CamBitter/bike-theft-deterrent-system.github.io/images/armedScreen.jpeg

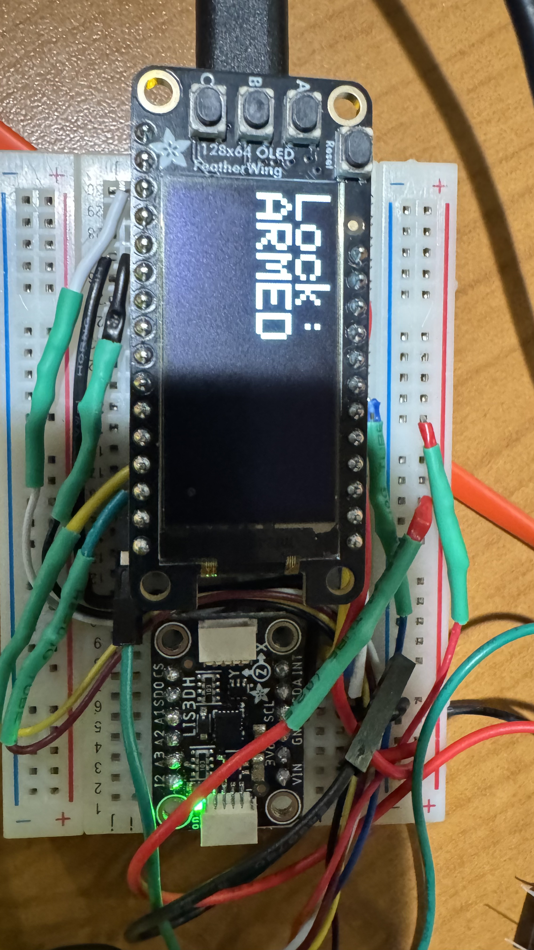
images/armedScreen.jpeg
