CamBitter/bike-theft-deterrent-system.github.io/images/boxWork.jpeg

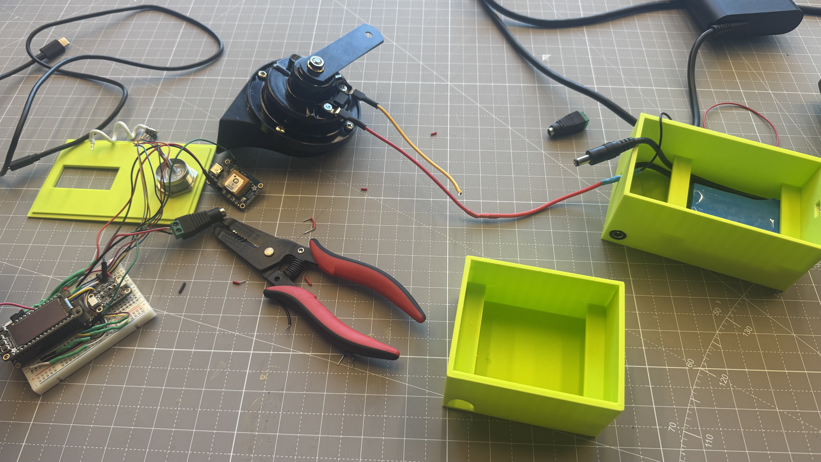
images/boxWork.jpeg
