CamBitter/bike-theft-deterrent-system.github.io/images/GPSwork.jpeg

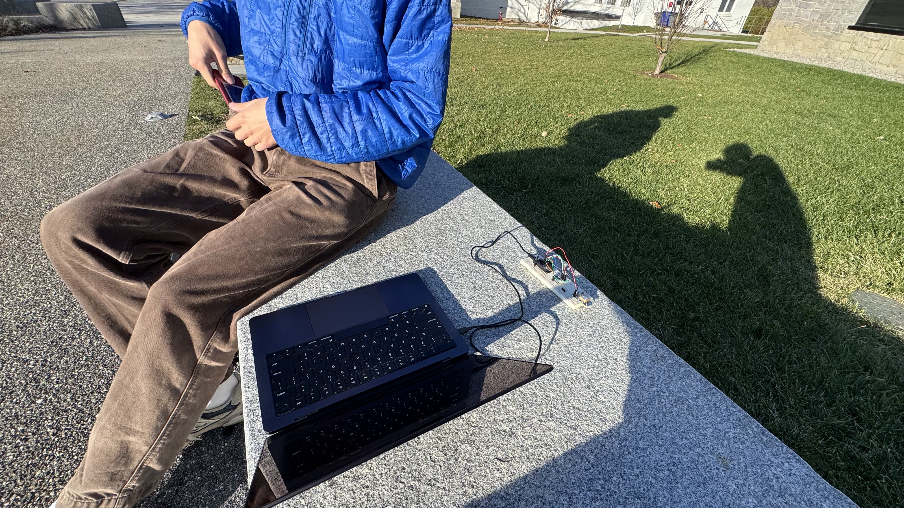
images/GPSwork.jpeg
