CamBitter/bike-theft-deterrent-system.github.io/images/procBomb.PNG

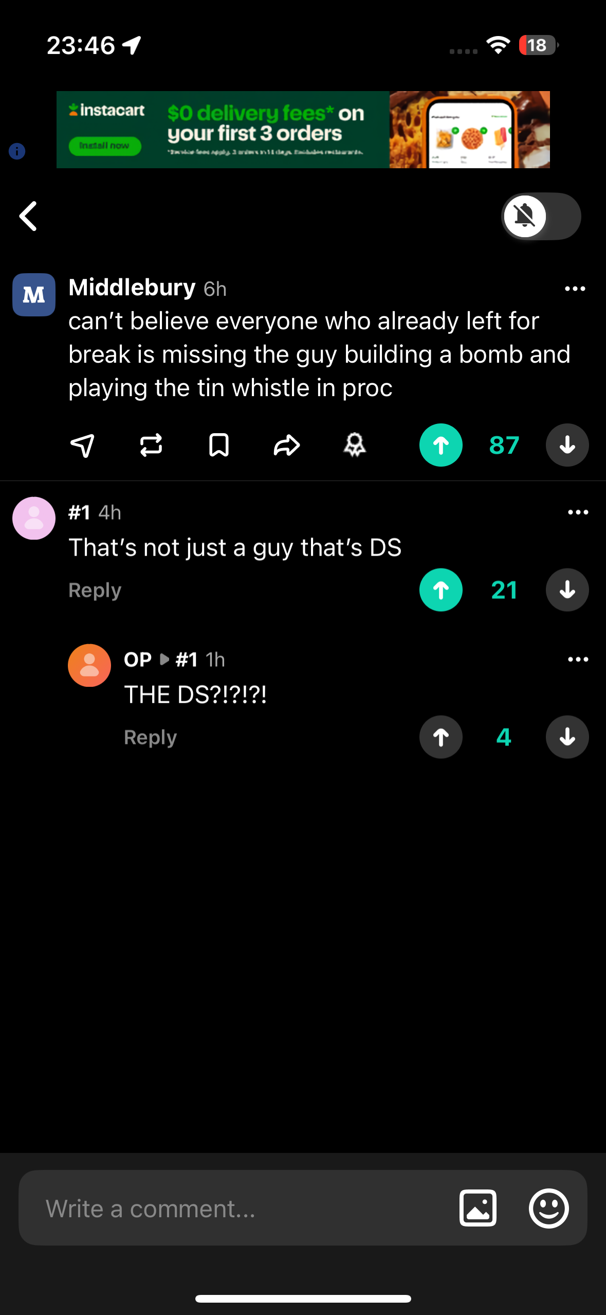
images/procBomb.PNG
