CamBitter/bike-theft-deterrent-system.github.io/src/mqtt.cpp

/*
 * Authors: Cam Bitter
 * MQTT client to push GPS data to Adafruit IO Dashboard
 */

#include <WiFi.h>
#include <Adafruit_MQTT.h>
#include <Adafruit_MQTT_Client.h>
#include "gps.h"
#include <esp_task_wdt.h>
#include "mqtt.h"
#include <stdlib.h>
#include "config.h"
#include "secrets.h"

const char *aio_url = "io.adafruit.com";
const uint16_t aio_port = 1883;
const char *gps_channel = "CamBitter/feeds/Bike-GPS/csv";

WiFiClient client;
Adafruit_MQTT_Client mqtt(&client, aio_url, aio_port, aio_username, aio_key);
Adafruit_MQTT_Publish gps_feed(&mqtt, gps_channel);

void MqttWifiKeepAlive(void *parameters)
{
  for (;;)
  {
    if (WiFi.status() != WL_CONNECTED)
    {
      Serial.println("[WiFi]: Connecting.");
      WiFi.begin(ssid, key);

      unsigned long startAttemptTime = millis();
      while (WiFi.status() != WL_CONNECTED && millis() - startAttemptTime < WIFI_TIMEOUT_MS)
      {
        vTaskDelay(250 / portTICK_PERIOD_MS);
      };
      if (WiFi.status() != WL_CONNECTED)
      {
        Serial.println("[WiFi]: Connection failed.");
        vTaskDelay(20000 / portTICK_PERIOD_MS);
        continue;
      }
      Serial.println("[WiFi]: Connected.");
    }

    if (WiFi.status() == WL_CONNECTED && !mqtt.connected())
    {

      Serial.println("[MQTT]: Connecting.");
      mqtt.connect();

      unsigned long startAttemptTime = millis();
      while (!mqtt.connected() && millis() - startAttemptTime < WIFI_TIMEOUT_MS)
      {
        vTaskDelay(250 / portTICK_PERIOD_MS); // prevent watchdog
      };
      if (!mqtt.connected())
      {
        Serial.println("[MQTT]: Connection failed.");
        vTaskDelay(20000 / portTICK_PERIOD_MS);
        continue;
      }
      Serial.println("[MQTT]: Connected.");
    }

    if (WiFi.status() == WL_CONNECTED && mqtt.connected())
    {
      mqtt.ping(); // ping server to keep connection alive
    }

    vTaskDelay(10000 / portTICK_PERIOD_MS);
  }
}

void startMqttWifiTask()
{
  xTaskCreatePinnedToCore(
      MqttWifiKeepAlive,
      "Keep MQTT and WiFi alive",
      15000,
      NULL,
      1,
      NULL,
      CONFIG_ARDUINO_RUNNING_CORE);
}

void publishGpsData(GPS_Data data)
{
  if (WiFi.status() != WL_CONNECTED)
  {
    Serial.println("[WiFi]: Not connected, skip publish.");
    return;
  }
  if (!mqtt.connected())
  {
    Serial.println("[MQTT]: Not connected, skip publish.");
    return;
  }
  char payload[100];
  char *p = payload;

  dtostrf(data.speed, 2, 6, p);
  p += strlen(p);
  *p++ = ',';

  dtostrf(data.latitude, 2, 6, p);
  p += strlen(p);
  *p++ = ',';

  dtostrf(data.longitude, 2, 6, p);
  p += strlen(p);
  *p++ = ',';

  dtostrf(data.altitude, 2, 6, p);
  p += strlen(p);

  *p = '\0';

  Serial.println("[MQTT]: Trying publish request...");

  if (gps_feed.publish(payload))
  {
    Serial.println("[MQTT]: Published request successfully. ");
  }
  else
  {
    Serial.println("[MQTT]: Publish failed.");
  }
}

bool isMqttConnected()
{
  return WiFi.status() == WL_CONNECTED && mqtt.connected();
}
